iotdevspot/max7219-driven-8-digit-7-segment-display-common-cathode/images/3.jpg

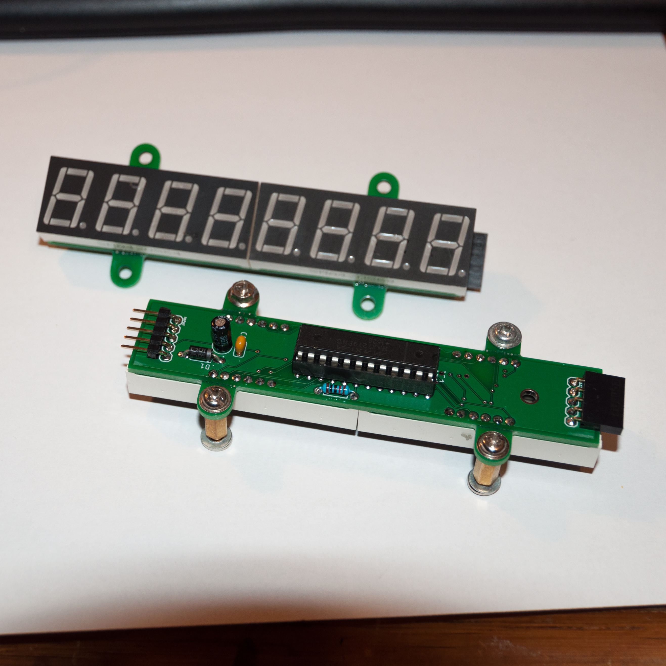
images/3.jpg
