iotdevspot/max7219-driven-8-digit-7-segment-display-common-cathode/images/4.jpg

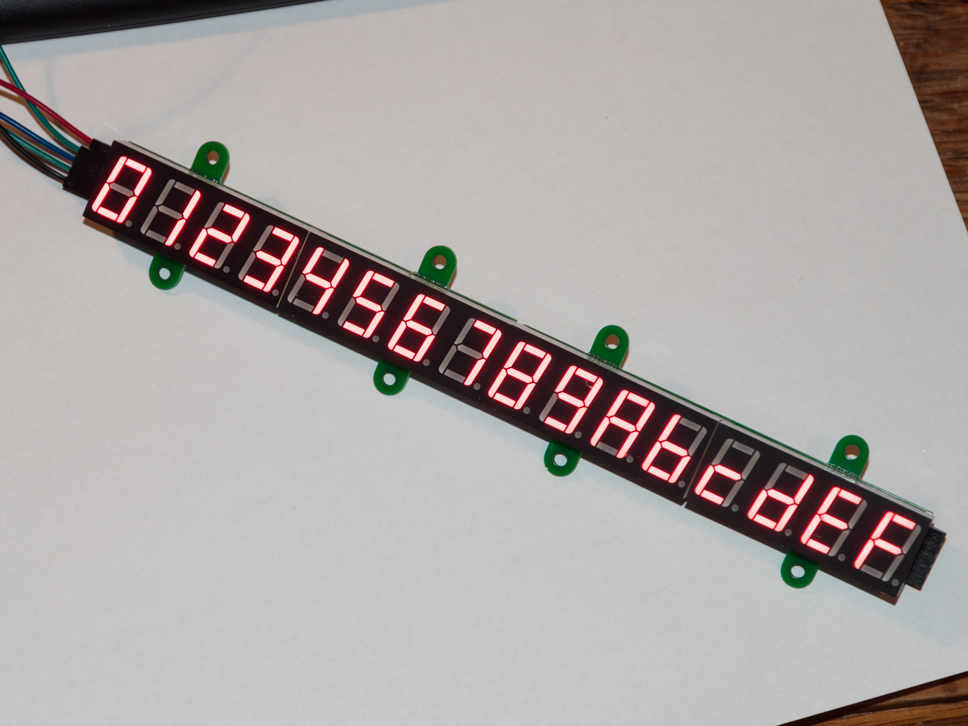
images/4.jpg
