iotdevspot/max7219-driven-8-digit-7-segment-display-common-cathode/images/6.jpg

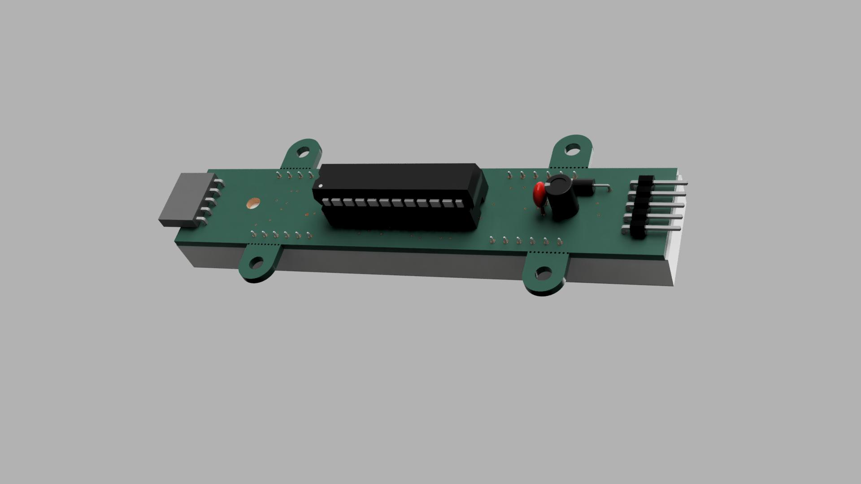
images/6.jpg
