iotdevspot/max7219-driven-8-digit-7-segment-display-common-cathode/images/10.PNG

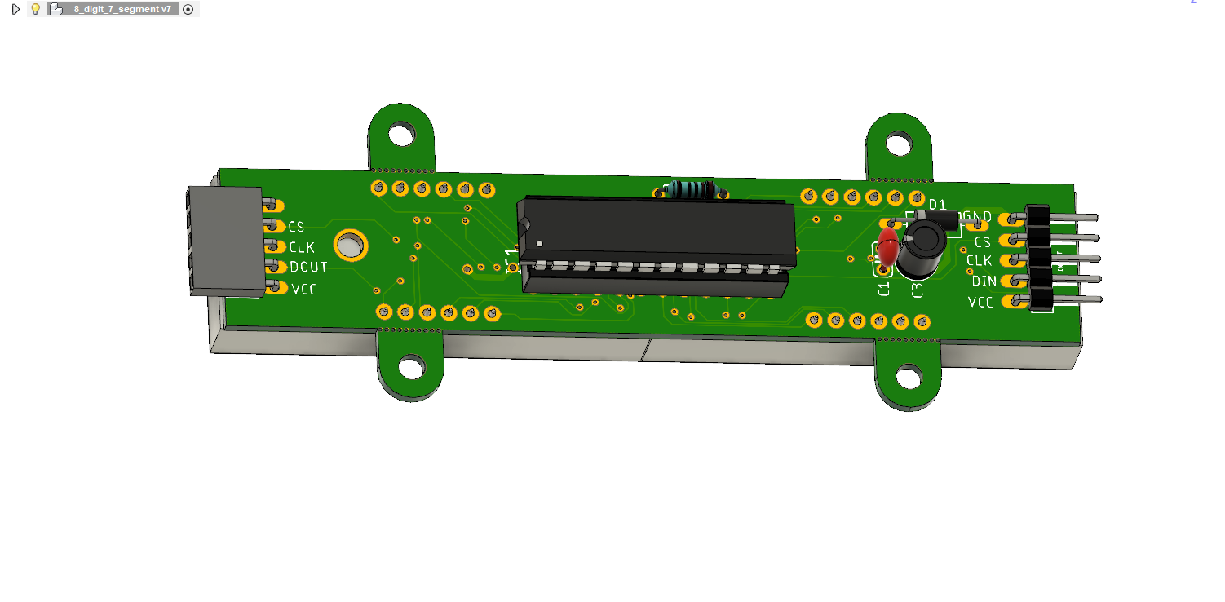
images/10.PNG
