iotdevspot/max7219-driven-8-digit-7-segment-display-common-cathode/images/11.PNG

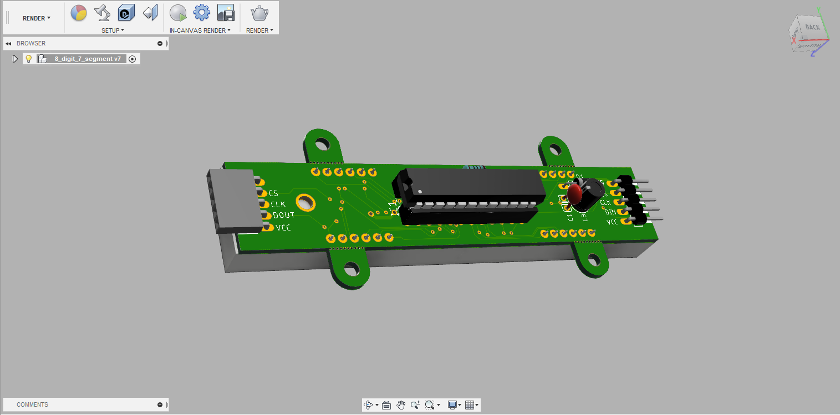
images/11.PNG
